shaynoorani/ECE4180_CANalyzer/schematic/schematic.kicad_sch

## KiCad design schematic/schematic.kicad_sch (2024-04-22)

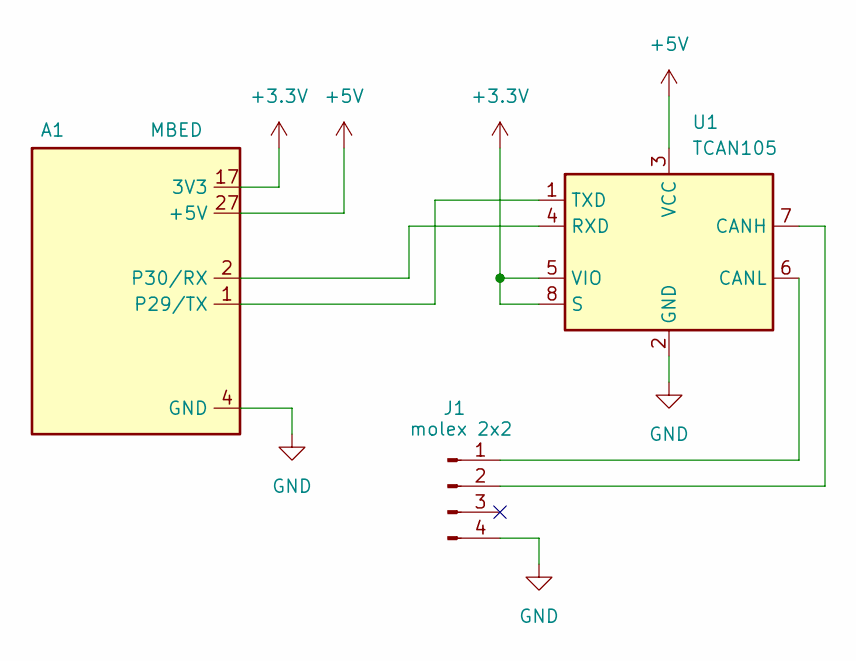
[picture p13: schematic schematic.kicad_sch]

Parts:
A1: MBED; Arduino_Nano
J1: molex 2x2
U1: TCAN105

Connections:
+3.3V: A1.17 (3V3), U1.5 (VIO), U1.8 (S)
+5V: A1.27 (+5V), U1.3 (VCC)
GND: A1.4 (GND), J1.4, U1.2 (GND)
unnamed: A1.1 (P29/TX), U1.1 (TXD)
unnamed: A1.2 (P30/RX), U1.4 (RXD)
unnamed: J1.1, U1.6 (CANL)
unnamed: J1.2, U1.7 (CANH)
